mackieks/thundervolt/software/firmware/src/gpio.h

/**
 * GPIO library for AVR 0/1-series MCUs.
 */

#pragma once

#include <avr/io.h>
#include <stdbool.h>

/**
 * Struct to represent an AVR pin
 */
typedef struct gpio {
  PORT_t *port;
  uint8_t num;
} gpio_t;

/**
 * Set the direction of a pin to output
 *
 * @param gpio The pin to set as an output
 */
static inline void gpio_output(gpio_t gpio)
{
  gpio.port->DIRSET = (1 << gpio.num);
}

/**
 * Set the direction of a pin to input
 *
 * @param gpio The pin to set as an input
 */
static inline void gpio_input(gpio_t gpio)
{
  gpio.port->DIRCLR = (1 << gpio.num);
}

/**
 * Configure the control settings for a pin
 *
 * @param gpio The pin to configure
 * @param ctrl The control settings to apply (see PORT_PINnCTRL in the datasheet)
 */
static inline void gpio_config(gpio_t gpio, uint8_t ctrl)
{
  (&gpio.port->PIN0CTRL)[gpio.num] = ctrl;
}

/**
 * Set a pin high
 *
 * @param gpio The pin to set high
 */
static inline void gpio_set_high(gpio_t gpio)
{
  gpio.port->OUTSET = (1 << gpio.num);
}

/**
 * Set a pin low
 *
 * @param gpio The pin to set low
 */
static inline void gpio_set_low(gpio_t gpio)
{
  gpio.port->OUTCLR = (1 << gpio.num);
}

/**
 * Toggle the state of a pin
 *
 * @param gpio The pin to toggle
 */
static inline void gpio_toggle(gpio_t gpio)
{
  gpio.port->OUTTGL = (1 << gpio.num);
}

/**
 * Read the state of a pin
 *
 * @param gpio The pin to read
 * @return The state of the pin
 */
static inline bool gpio_read(gpio_t gpio)
{
  return (gpio.port->IN & (1 << gpio.num));
}

/**
 * Read the state of an interrupt flag
 *
 * @param gpio The pin to read the interrupt flag for
 * @return The state of the interrupt flag
 */
static inline bool gpio_read_intflag(gpio_t gpio)
{
  return (gpio.port->INTFLAGS & (1 << gpio.num));
}
