mackieks/thundervolt/software/homebrew/source/assets.h

#pragma once

// Font
#include "Glass_TTY_VT220_ttf.h"

// Image
#include "arrow_png.h"
#include "bullet_png.h"
#include "cursor_png.h"
#include "dolphin_png.h"
#include "note_png.h"
#include "toggle_off_png.h"
#include "toggle_on_png.h"
#include "tv_png.h"

// SFX
#include "back_raw.h"
#include "enter_raw.h"
#include "move_raw.h"

// Music
#include "sample_mp3.h"
